Individual-Solid/B36502X/eaterexperiment/output/3dlayout.PNG

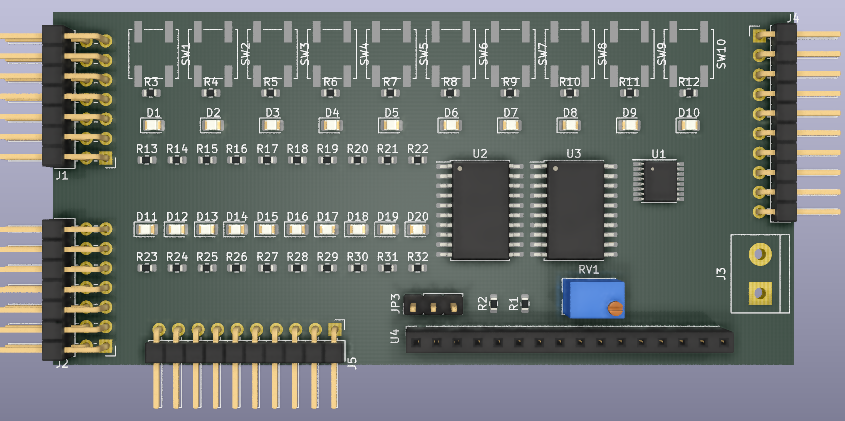
eaterexperiment/output/3dlayout.PNG
