Individual-Solid/B36502X/02xsbcfirst/output/3d layout.PNG

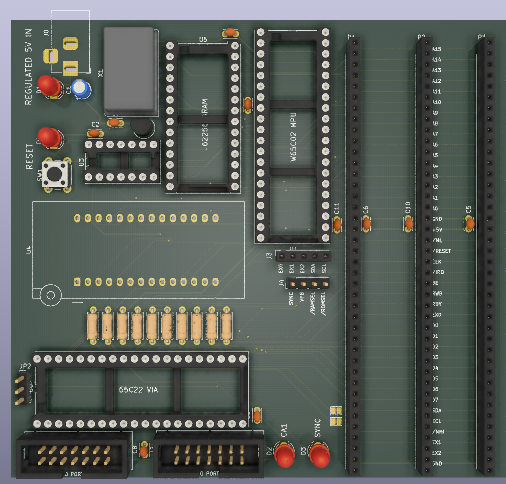
02xsbcfirst/output/3d layout.PNG
