Individual-Solid/B36502X/02xsbcfirst/output/IMG_0706.jpg

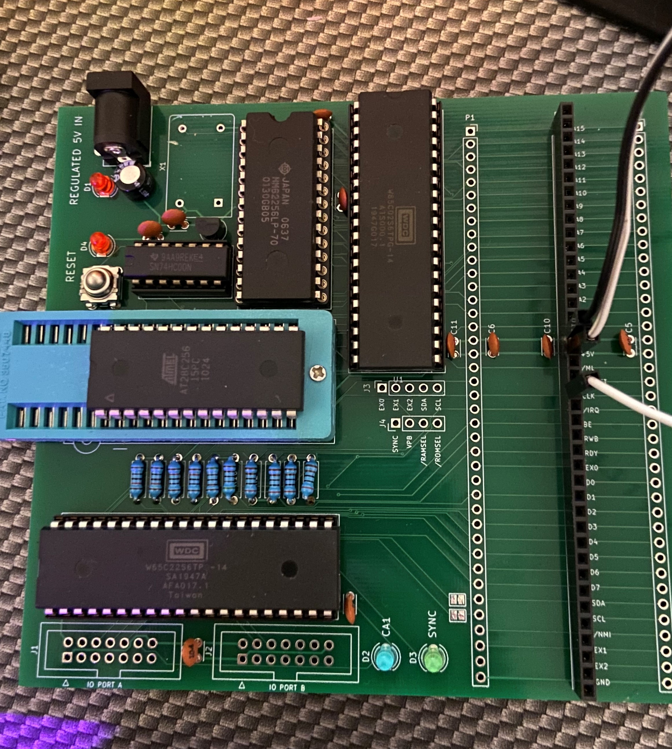
02xsbcfirst/output/IMG_0706.jpg
