Individual-Solid/B36502X/02xsbcfirst/output/schematic2.png

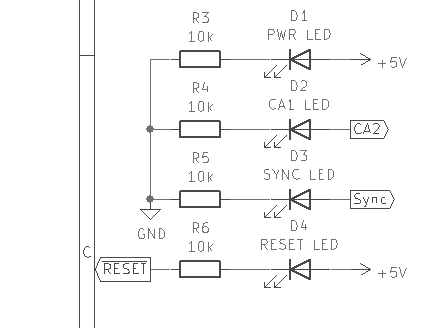
02xsbcfirst/output/schematic2.png
