Individual-Solid/B36502X/02xsbcfirst/output/schematic.png

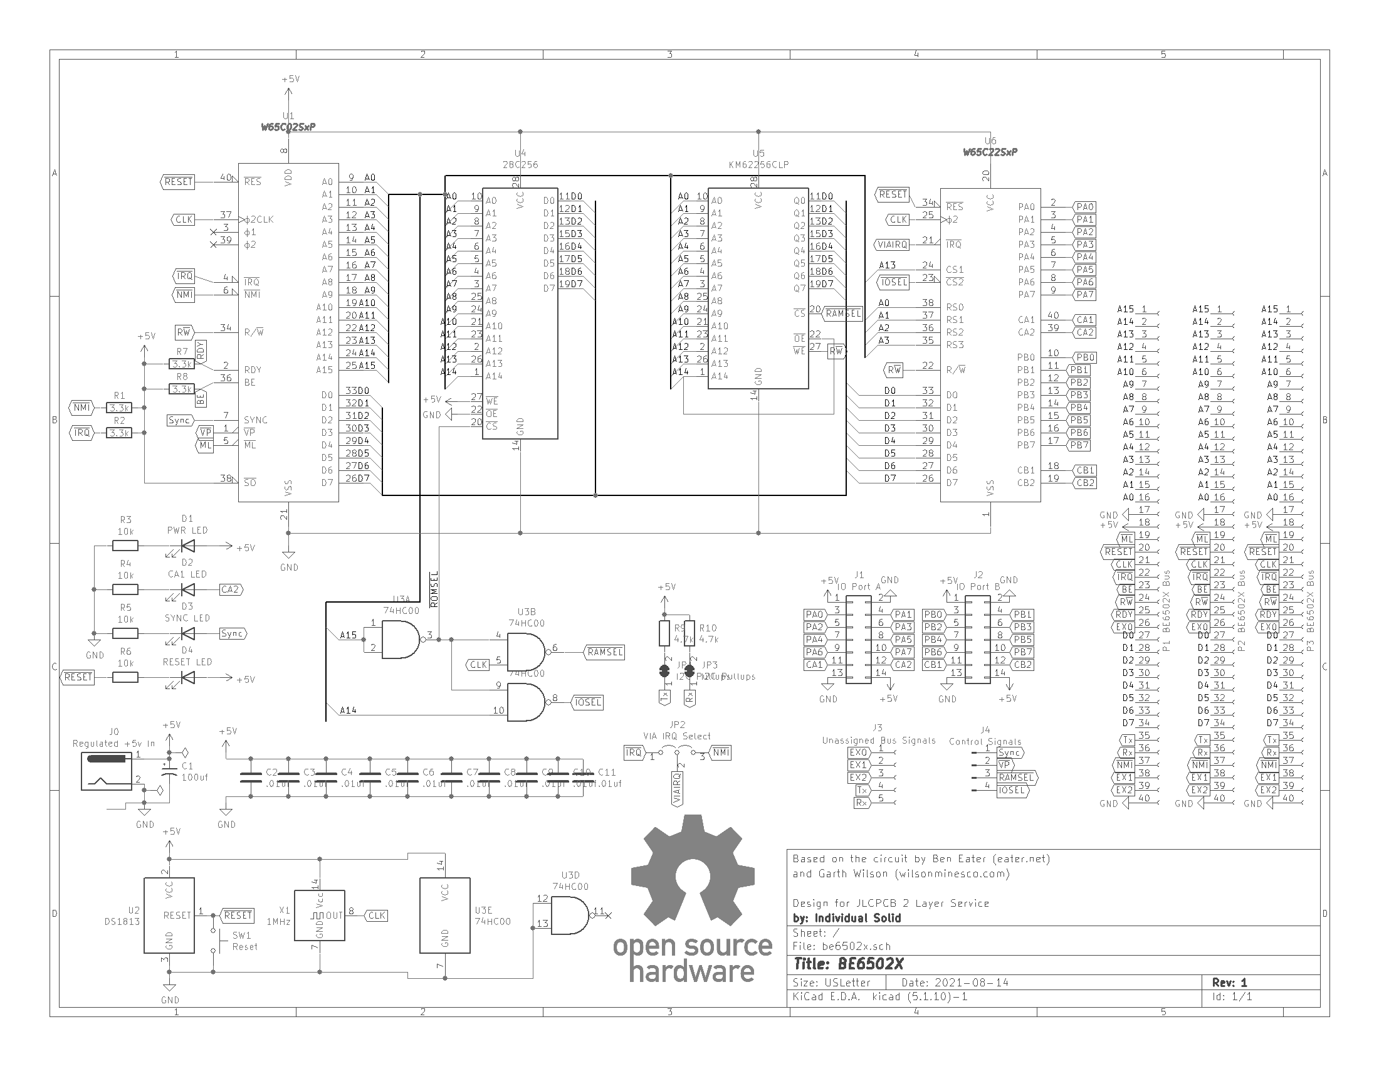
02xsbcfirst/output/schematic.png
