Individual-Solid/B36502X/eaterexperiment/output/schematic.png

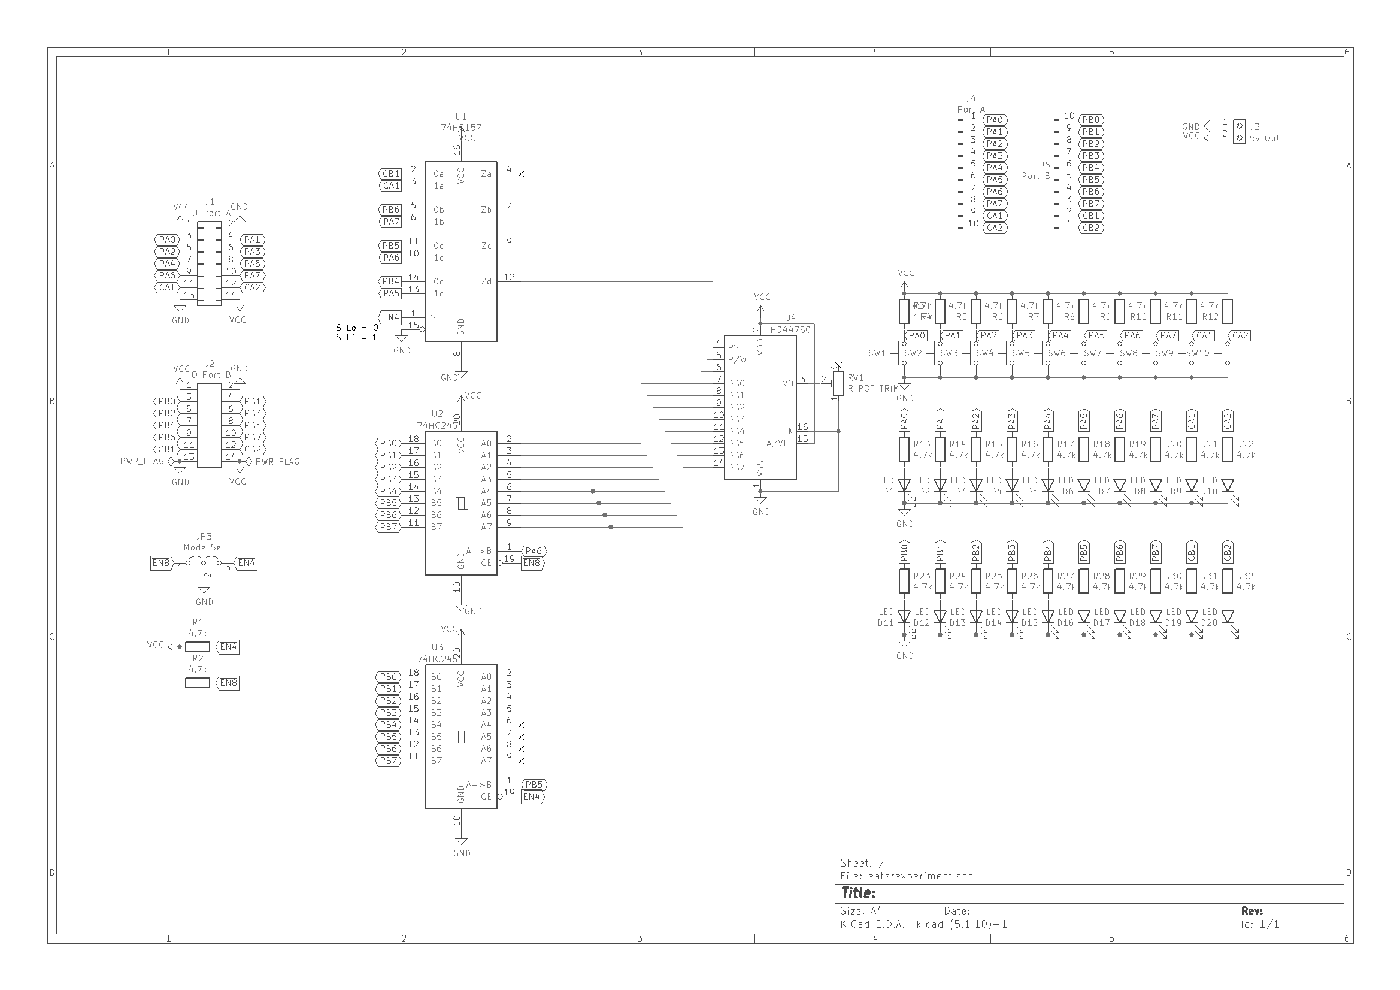
eaterexperiment/output/schematic.png
