Individual-Solid/B36502X/02xsbcfirst/output/scope traces/slow power on reset/DS1Z_QuickPrint2.png

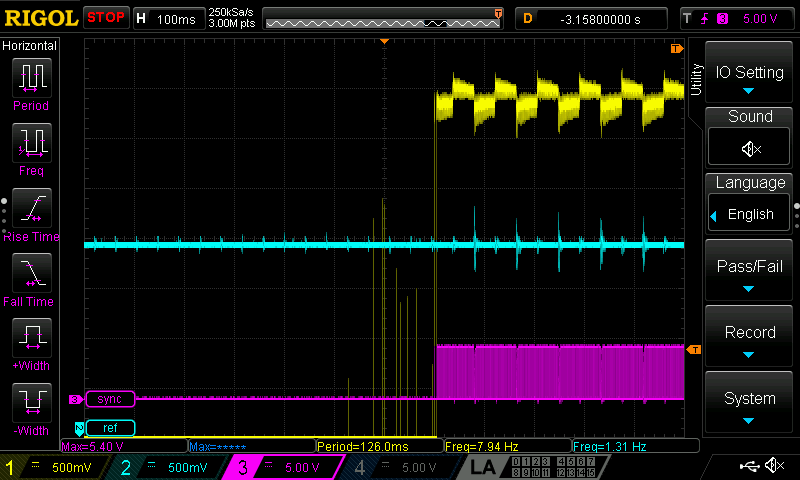
02xsbcfirst/output/scope traces/slow power on reset/DS1Z_QuickPrint2.png
