Individual-Solid/B36502X/02xsbcfirst/output/scope traces/slow power on reset/DS1Z_QuickPrint4.png

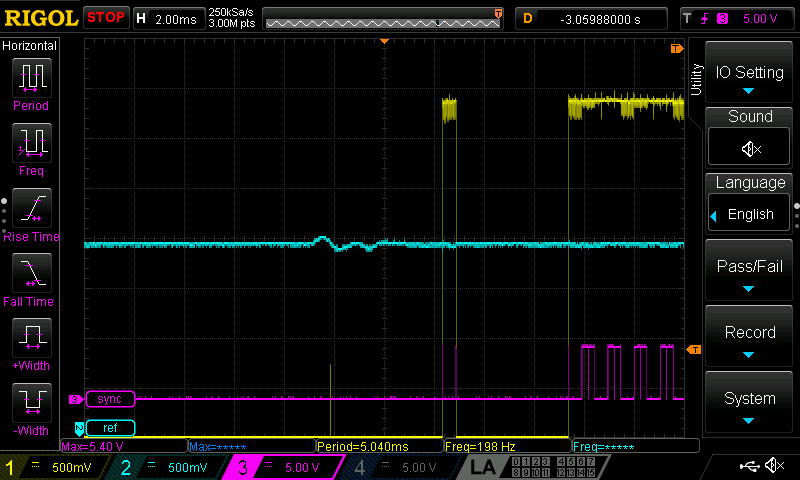
02xsbcfirst/output/scope traces/slow power on reset/DS1Z_QuickPrint4.png
