Individual-Solid/B36502X/02xsbcfirst/output/scope traces/slow power on reset/DS1Z_QuickPrint5.png

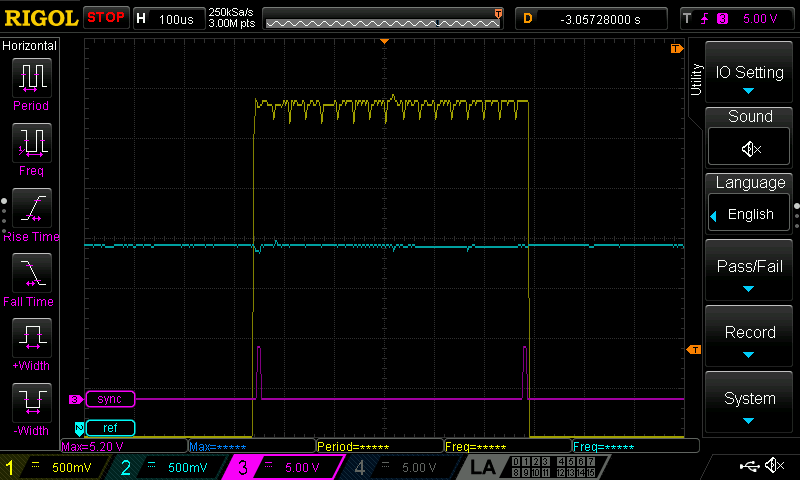
02xsbcfirst/output/scope traces/slow power on reset/DS1Z_QuickPrint5.png
